joao-pinheiro/atx_psu/enclosure/front_panel.scad

include <enclosure.scad>

// Render front panel
frontPlate();
