joao-pinheiro/atx_psu/enclosure/test_plate.scad

include <enclosure.scad>

// Test holes for front panel instruments
testPlate();
